vcazan/open-screen-deck/docs/images/pcb-3d-bottom.png

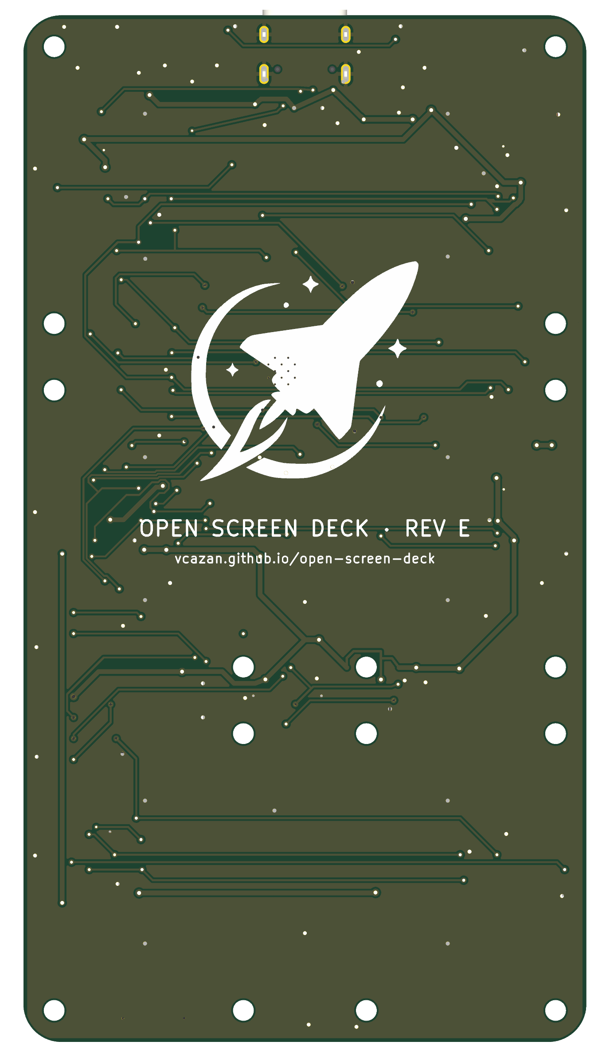
docs/images/pcb-3d-bottom.png
