vcazan/open-screen-deck/docs/reference/screenkey-module/vendor-dimensions.png

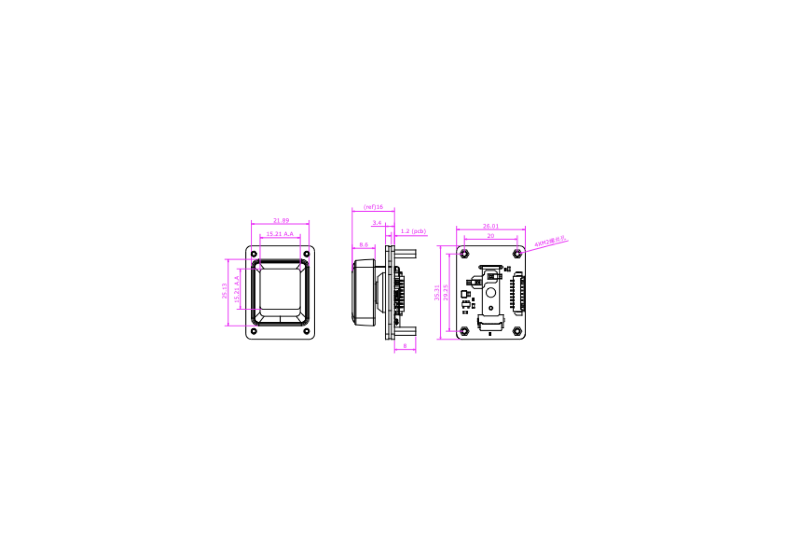
docs/reference/screenkey-module/vendor-dimensions.png
