vcazan/open-screen-deck/previews/enclosure-front.png

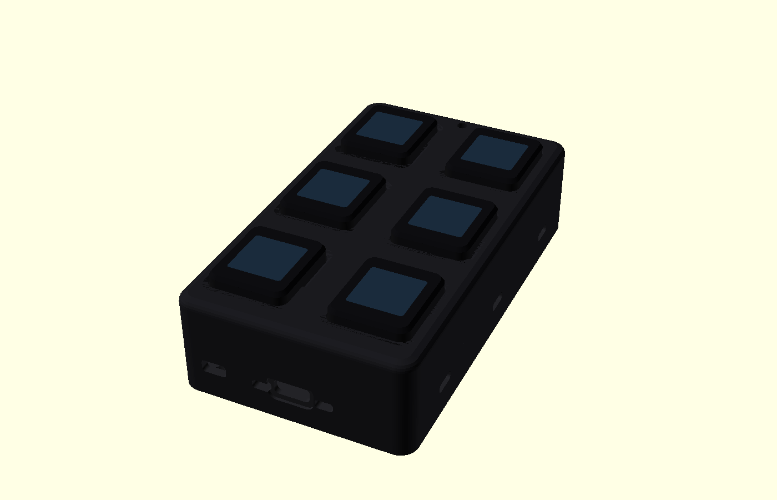
previews/enclosure-front.png
