vcazan/open-screen-deck/previews/final_bottom.png

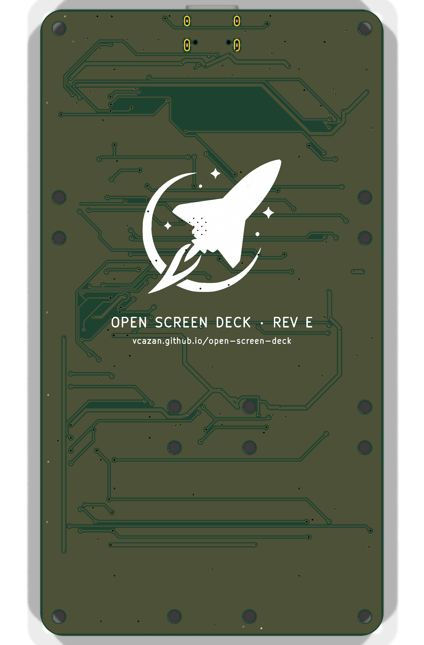
previews/final_bottom.png
