vcazan/open-screen-deck/previews/final_iso.png

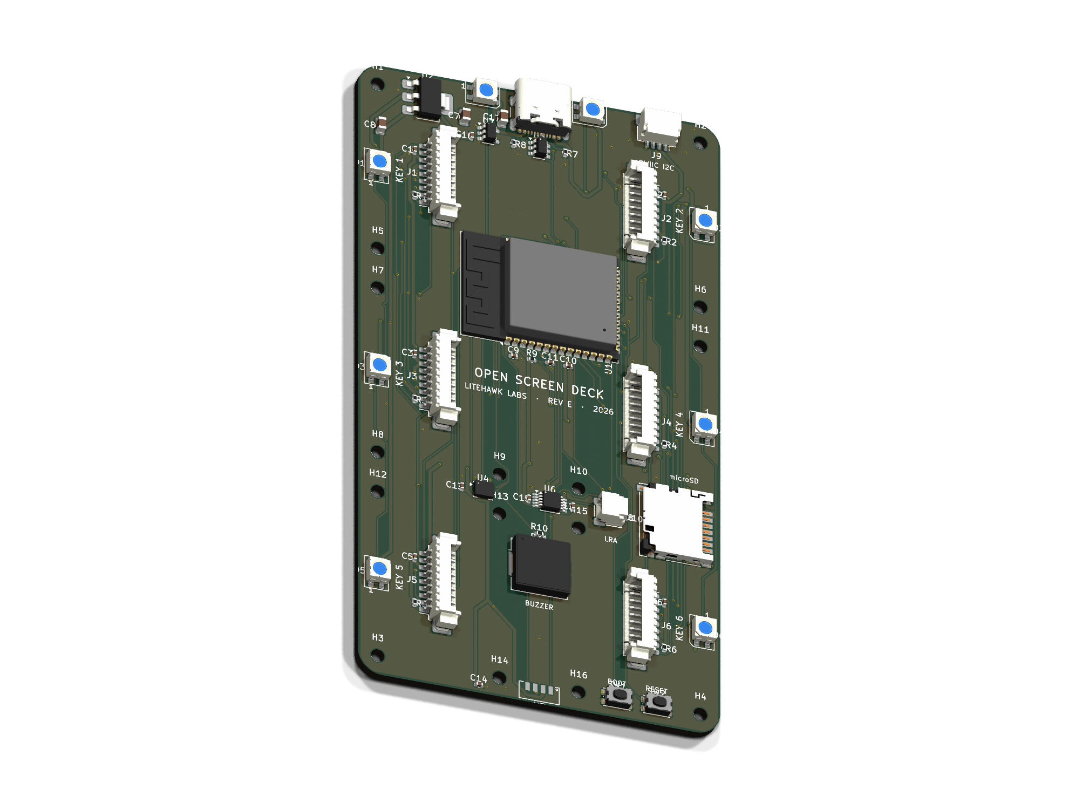
previews/final_iso.png
