vcazan/open-screen-deck/previews/fusion_v11_corner_aligned.png

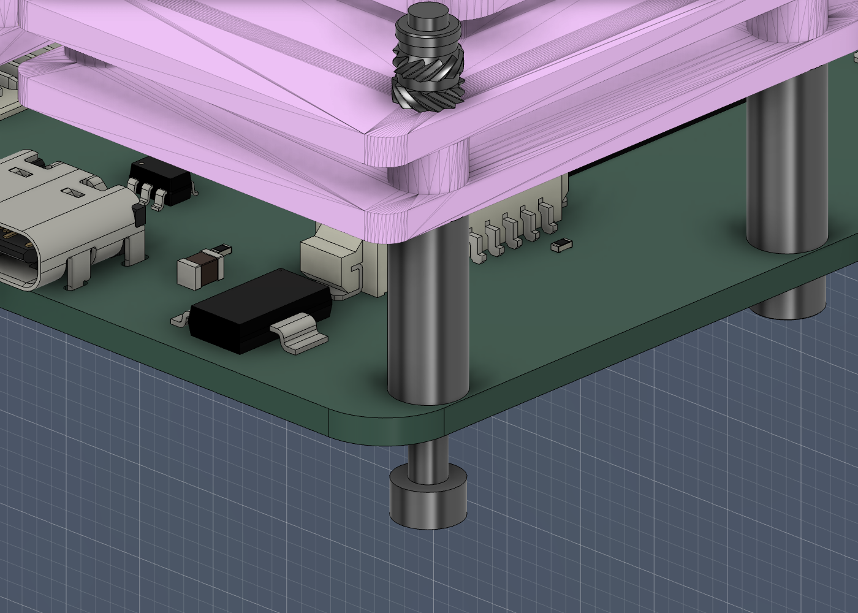
previews/fusion_v11_corner_aligned.png
