vcazan/open-screen-deck/previews/fusion_v11_hero.png

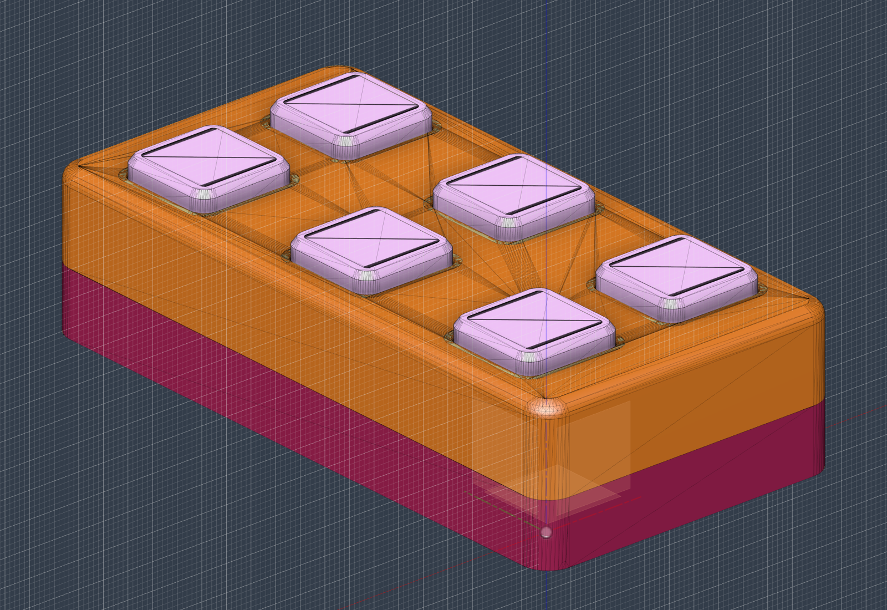
previews/fusion_v11_hero.png
