vcazan/open-screen-deck/previews/pcb-bottom.png

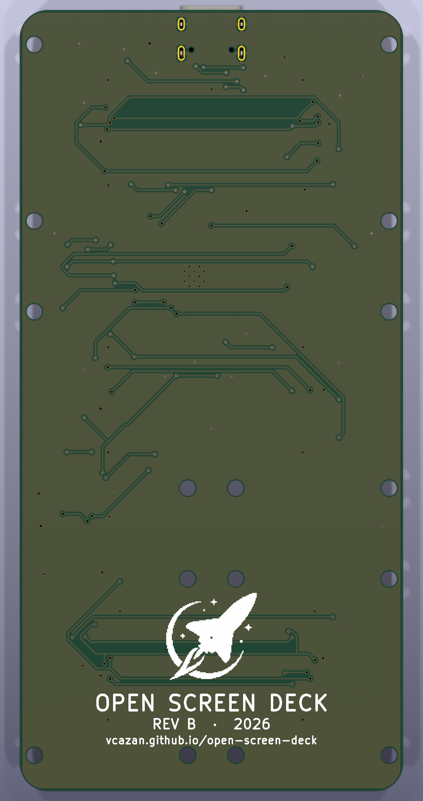
previews/pcb-bottom.png
