vcazan/open-screen-deck/previews/pcb-top.png

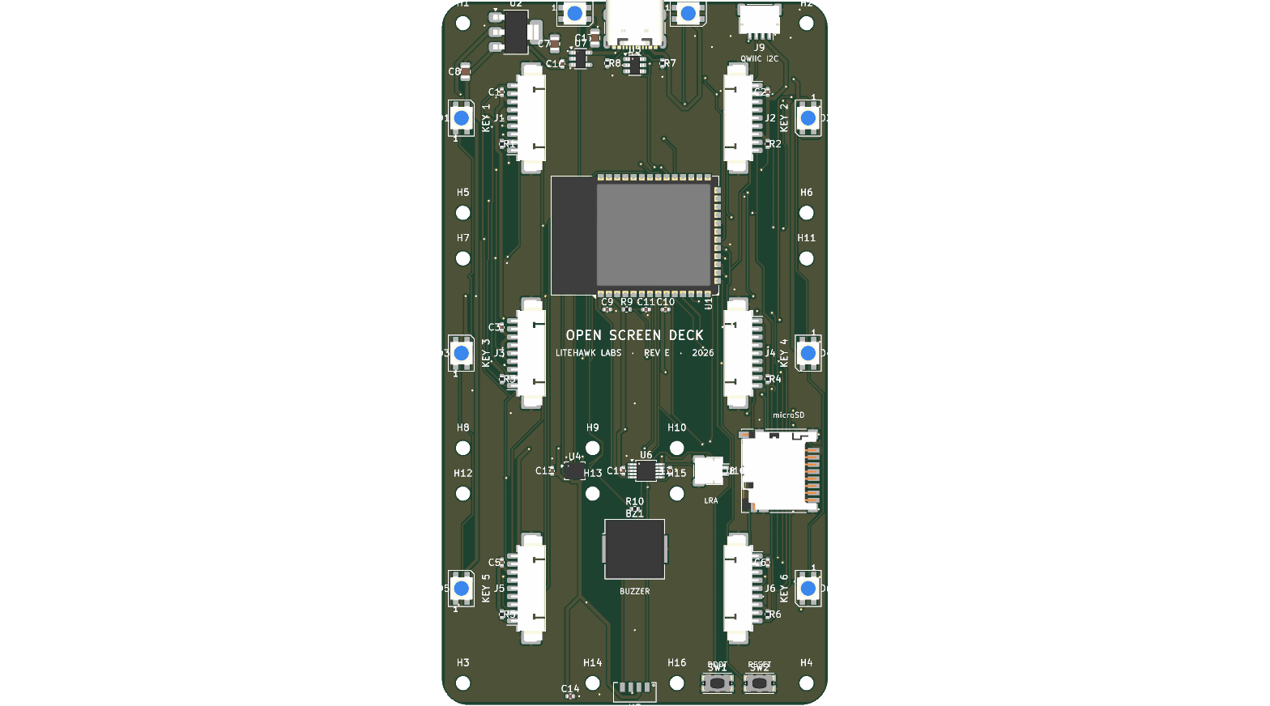
previews/pcb-top.png
