vcazan/open-screen-deck/previews/render_hero.png

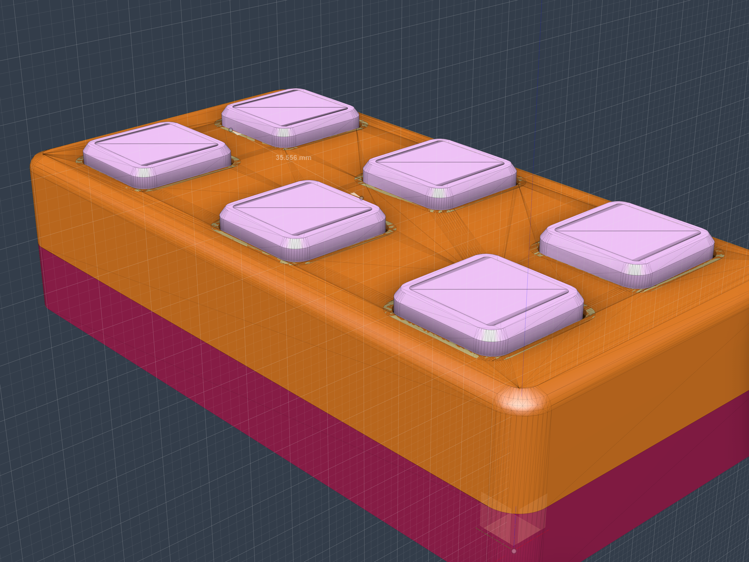
previews/render_hero.png
