vcazan/open-screen-deck/previews/render_rear.png

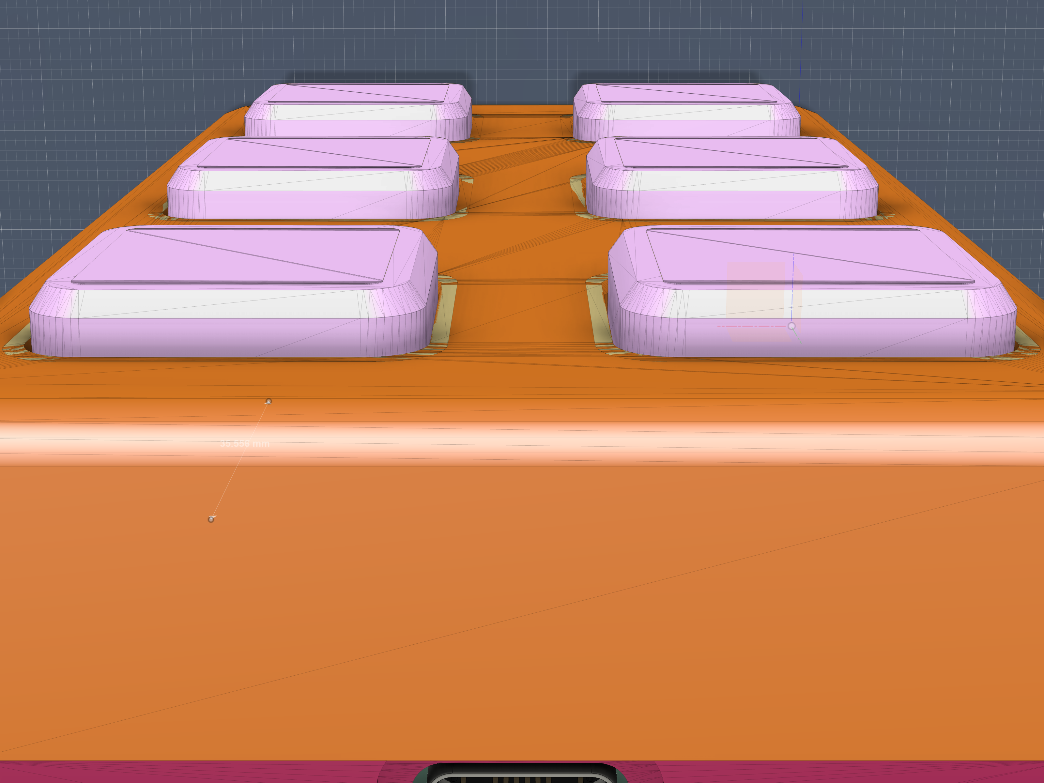
previews/render_rear.png
