vcazan/open-screen-deck/previews/render_side.png

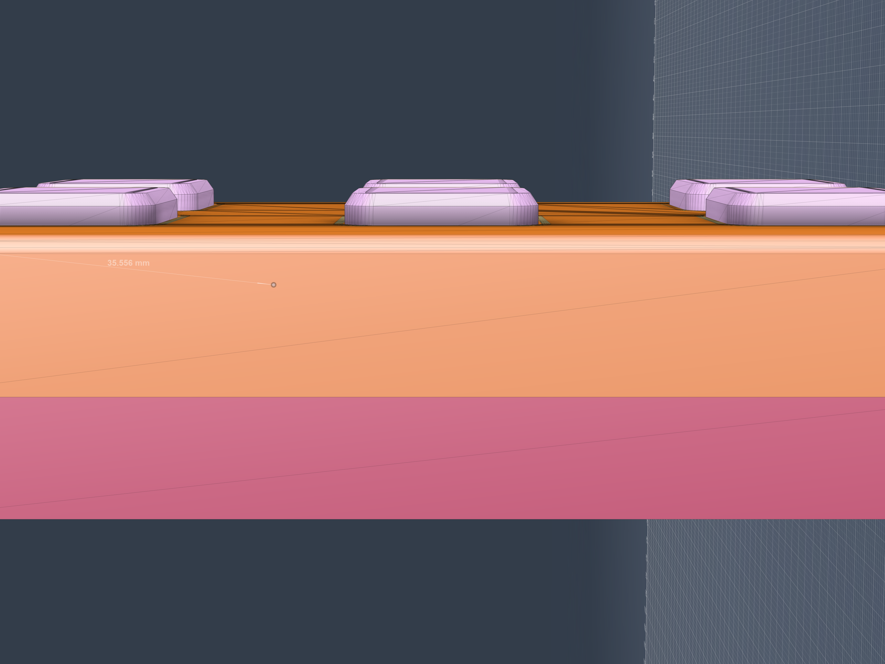
previews/render_side.png
