vcazan/open-screen-deck/previews/render_top_ortho.png

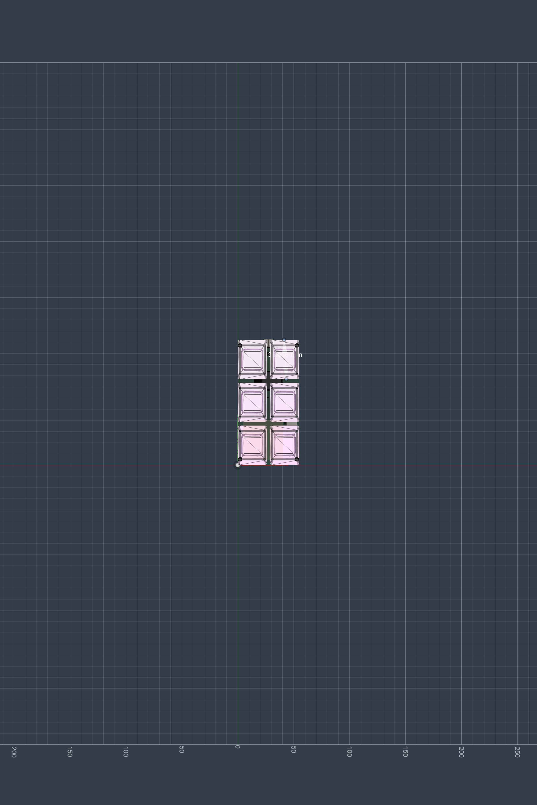
previews/render_top_ortho.png
