vcazan/open-screen-deck/previews/screenkey-module-v2.png

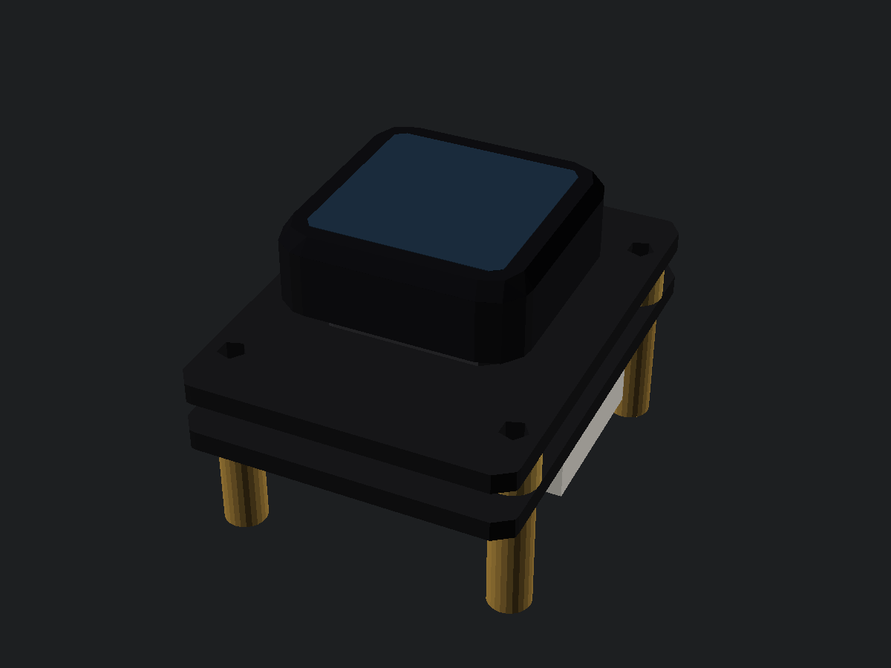
previews/screenkey-module-v2.png
