vcazan/open-screen-deck/firmware/pages.cpp

#include "pages.h"
#include "state.h"
#include "display.h"
#include "media.h"

uint8_t currentPage = 0;
uint8_t pageCount   = 1;

void savePagePref() {
    prefs.begin("osd", false);
    prefs.putUChar("page", currentPage);
    prefs.putUChar("pages", pageCount);
    prefs.end();
}

void switchPage(uint8_t page) {
    if (page >= pageCount) return;
    stopAnimation();
    if (page == currentPage) {
        if (Serial) Serial.printf("{\"event\":\"page\",\"page\":%u}\n", currentPage);
        return;
    }
    currentPage = page;
    // Draw all six under a dark backlight, then fade in together — never
    // blit keys one-by-one (scheduleDrawAll would leave a 350 ms window
    // where live SET_FACE updates stagger across the page).
    drawAllVisible();
    savePagePref();
    if (Serial) Serial.printf("{\"event\":\"page\",\"page\":%u}\n", currentPage);
}

void setPageCount(uint8_t n) {
    if (n < 1 || n > MAX_PAGES || n == pageCount) return;
    if (n < pageCount) {
        // Dropped slots reset so a re-added page starts fresh
        for (uint8_t s = n * KEY_COUNT; s < pageCount * KEY_COUNT; s++) {
            defaultSlotConfig(s);
            saveConfig(s);
        }
    }
    pageCount = n;
    if (currentPage >= pageCount) {
        switchPage(pageCount - 1);   // also persists both prefs
    } else {
        savePagePref();
    }
    if (Serial) Serial.printf("{\"event\":\"pages\",\"pages\":%u}\n", pageCount);
}
